andreamazzitelli/checkBin/img/circuit.png

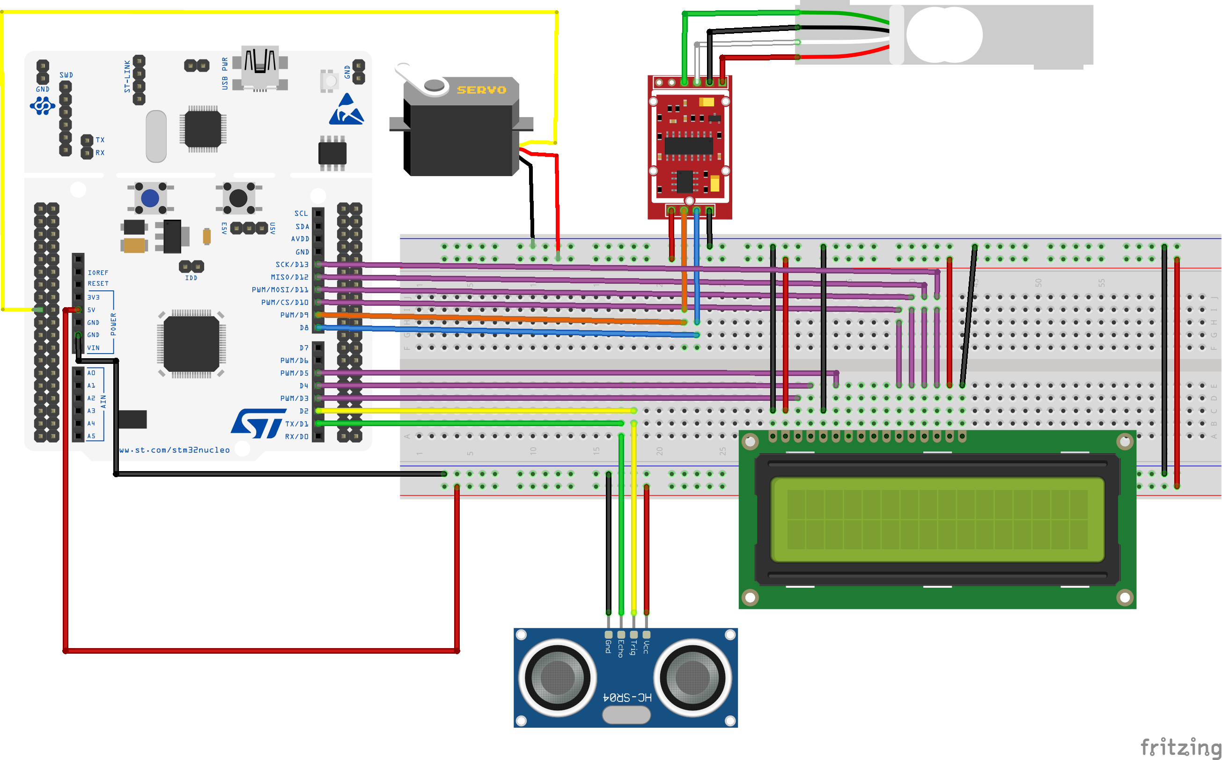
img/circuit.png
