andreamazzitelli/checkBin/img/ina_senza_oled.png

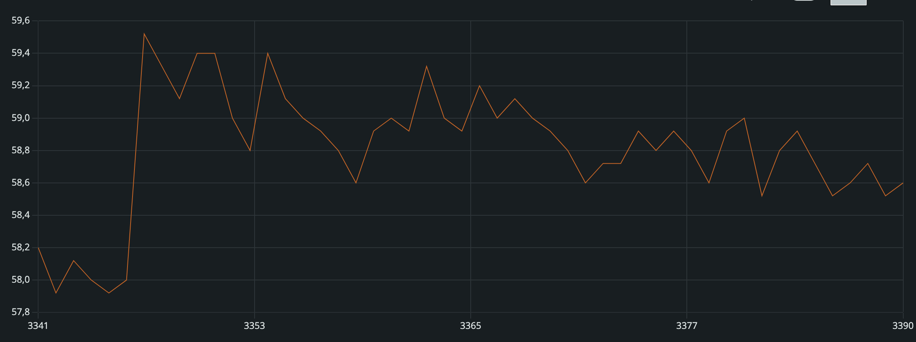
img/ina_senza_oled.png
