andreamazzitelli/checkBin/img/pins/green-pin.png

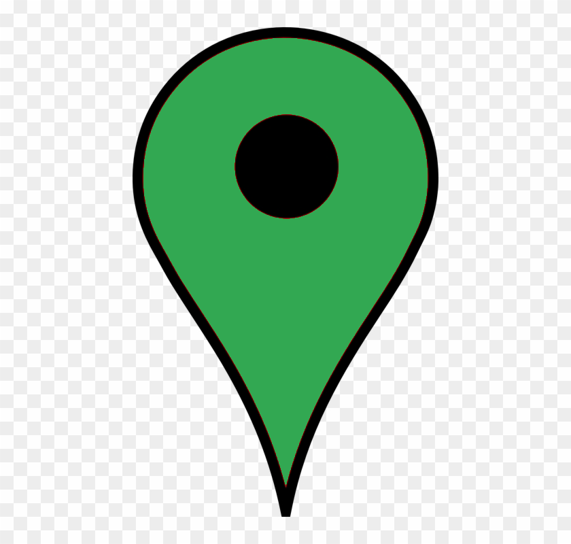
img/pins/green-pin.png
