andreamazzitelli/checkBin/img/pins/red-pin.png

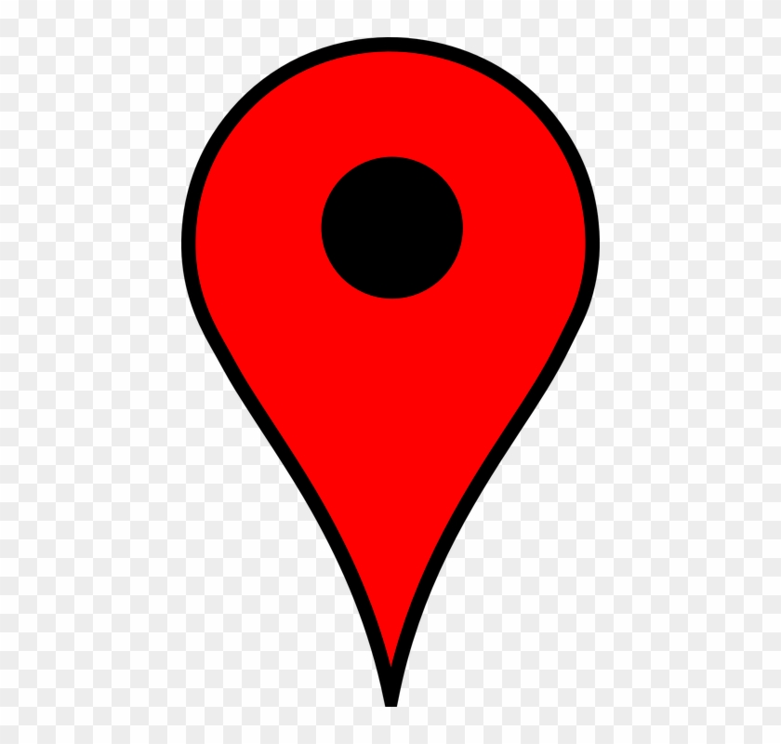
img/pins/red-pin.png
