andreamazzitelli/checkBin/img/pins/yellow-pin.png

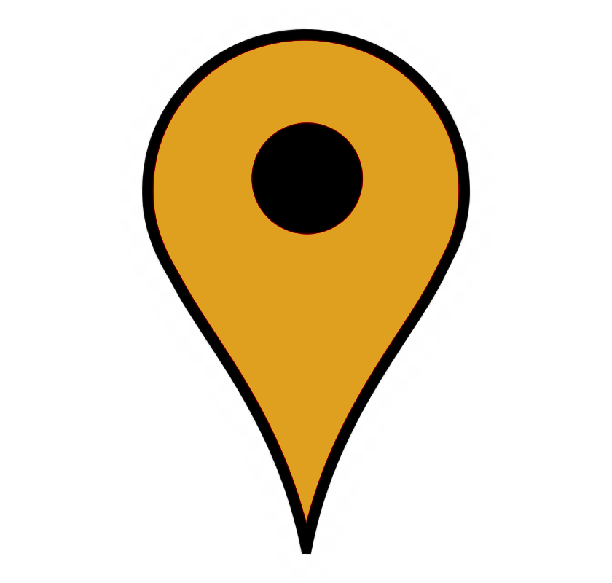
img/pins/yellow-pin.png
