andreamazzitelli/checkBin/RiotCode/main.h

#ifndef MAIN_FUNCTIONS
#define MAIN_FUNCTIONS

void echo_cb(void* arg);
int read_distance(void);
void set_stepper(int flag);
unsigned long read_weight(void);
void write_oled(char* message, int level);
void *open_button(void *arg);
int loramac_setup(char *deui, char *aeui, char *akey, char *xdr);
int loramac_send(char *message);
void components_init(void);

//define WASTE_TYPE = PLASTIC 0 | METAL 1 | GLASS 2 | PAPER 3 | FOOD 4 | MIXED 5
#define WASTE_TYPE 3
//define LoRa configuration parameters
#define DEVEUI "70B3D57ED004E9C9"
#define APPEUI "0000000000000000"
#define APPKEY "ACF56E9005262992A0D06E5C42192FD7"
//define bin height
#define MAX_DISTANCE 45
//define area in square meters
#define AREA 0.05

#define WASTE_TYPE_PLASTIC 0
#define WASTE_TYPE_METAL 1
#define WASTE_TYPE_GLASS 2
#define WASTE_TYPE_PAPER 3
#define WASTE_TYPE_FOOD 4
#define WASTE_TYPE_MIXED 5

#endif
